shiva233/HackCharm/Animations/DizzyFace.png

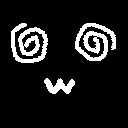
Animations/DizzyFace.png
