shiva233/HackCharm/Animations/HackCharmOwO.png

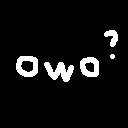
Animations/HackCharmOwO.png
