shiva233/HackCharm/Animations/SleepFace.gif

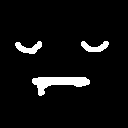
Animations/SleepFace.gif
